antmicro/scalenode-cm4-baseboard/assets/previews/layer1.png

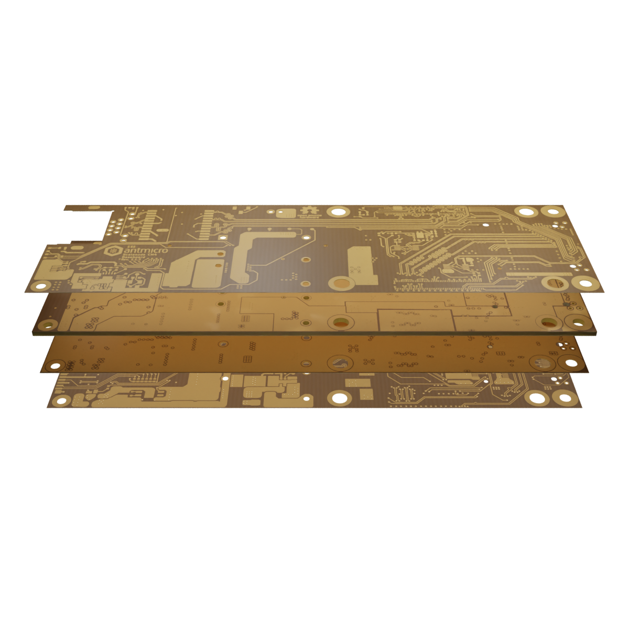
assets/previews/layer1.png
