antmicro/scalenode-cm4-baseboard/assets/previews/layer2.png

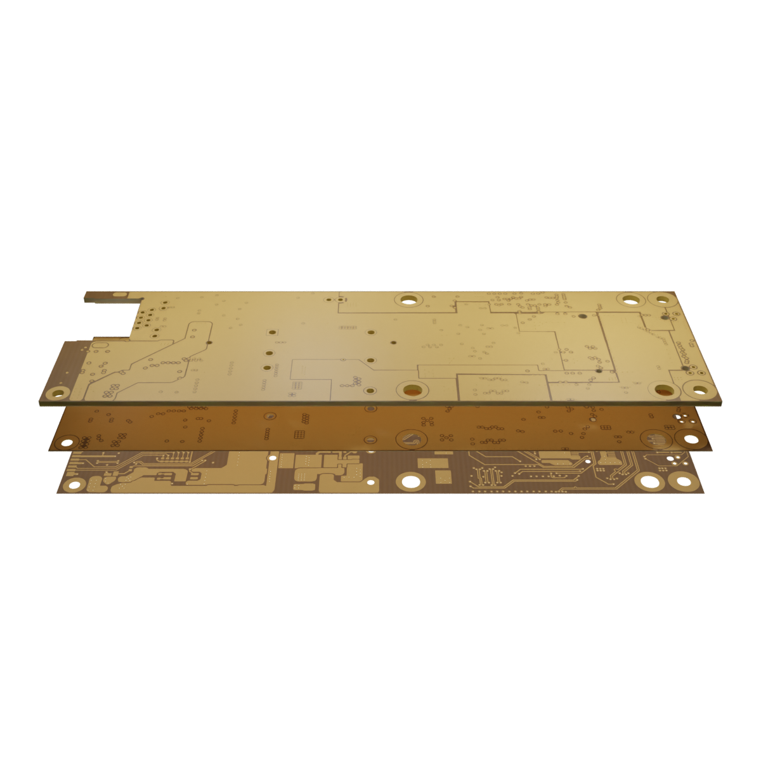
assets/previews/layer2.png
