antmicro/scalenode-cm4-baseboard/assets/previews/layer4.png

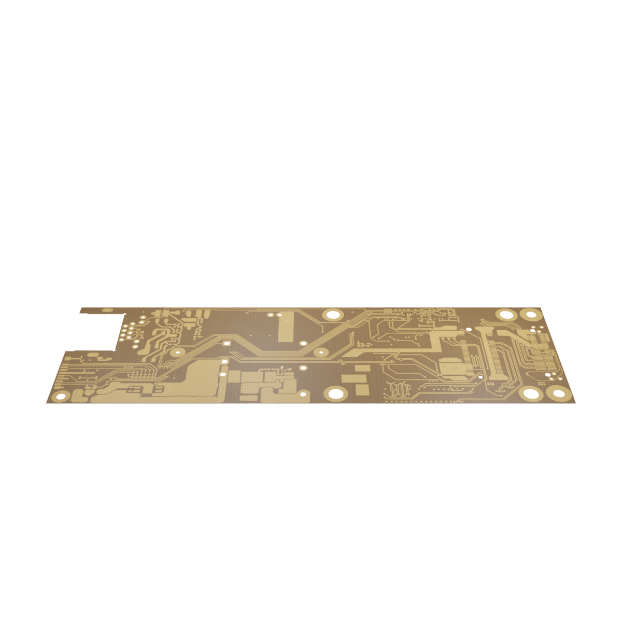
assets/previews/layer4.png
