antmicro/scalenode-cm4-baseboard/assets/previews/leftB.png

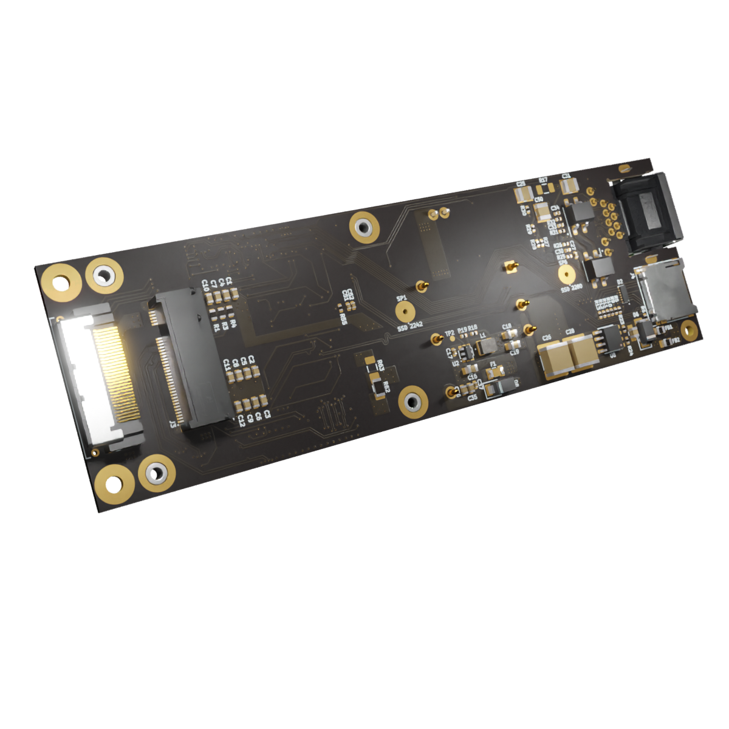
assets/previews/leftB.png
