antmicro/scalenode-cm4-baseboard/assets/previews/orthoB.png

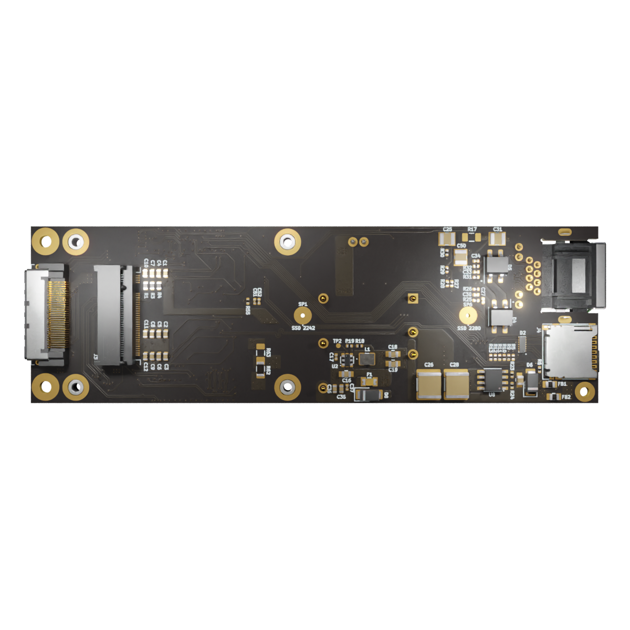
assets/previews/orthoB.png
