antmicro/scalenode-cm4-baseboard/assets/previews/orthoT.png

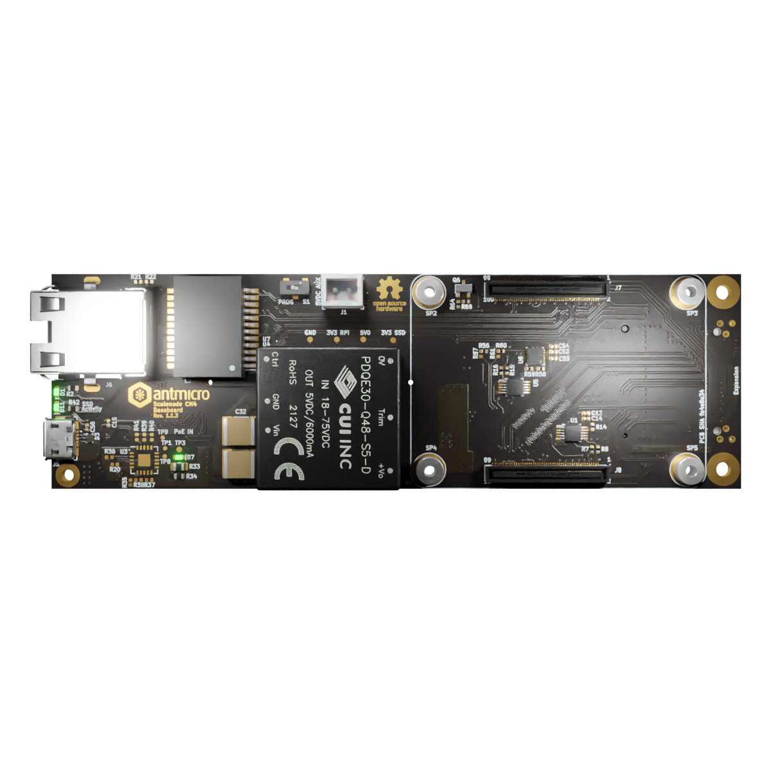
assets/previews/orthoT.png
