antmicro/scalenode-cm4-baseboard/assets/previews/rightB.png

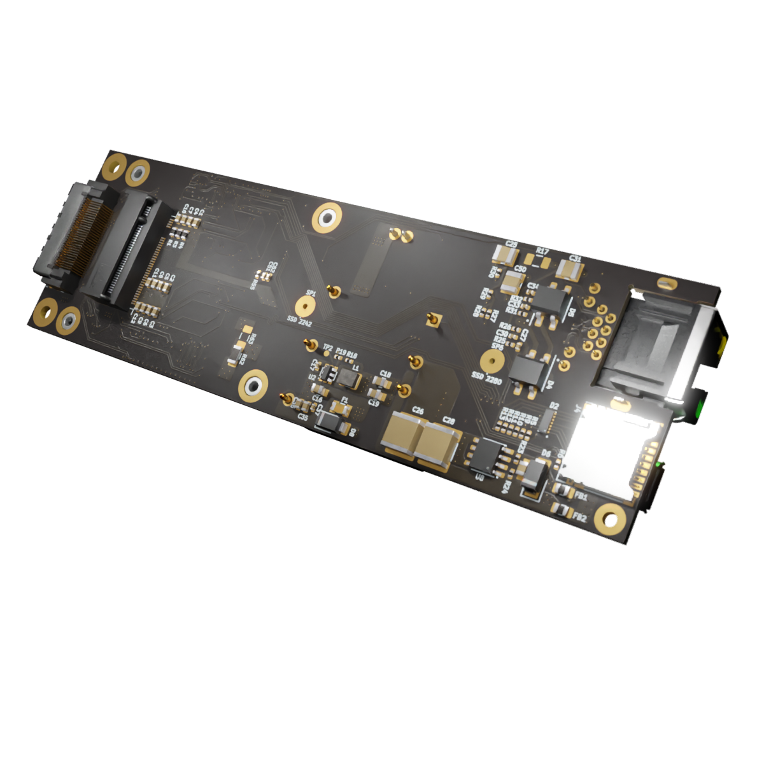
assets/previews/rightB.png
