antmicro/scalenode-cm4-baseboard/assets/previews/rightT.png

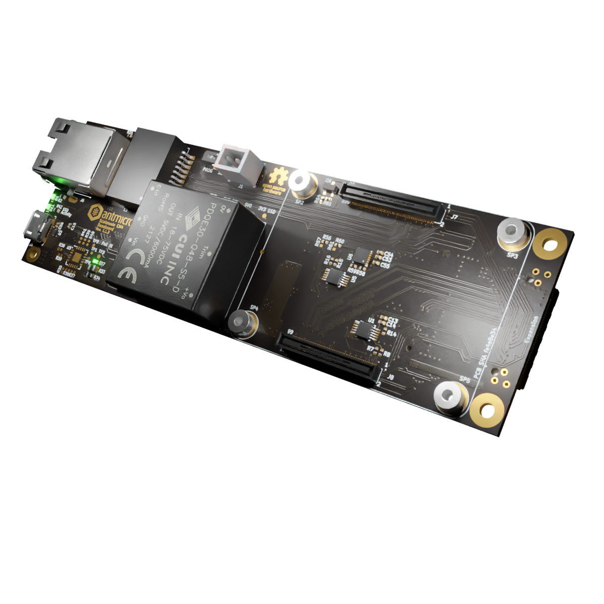
assets/previews/rightT.png
